esb8/4in-ECM/kicad/models/X322516MLB4SI.step

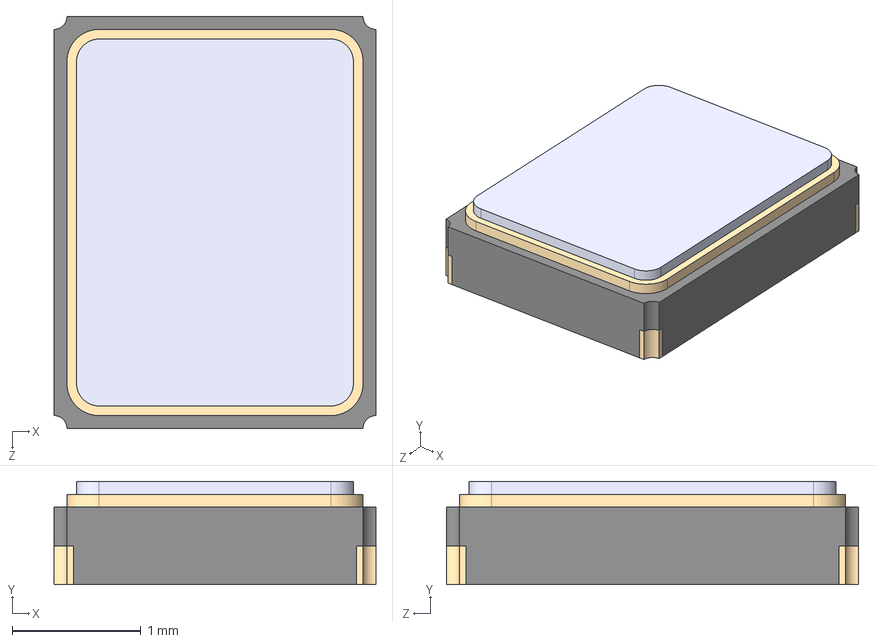
[picture p17: CAD file, 2025-09-10]
kicad/models/X322516MLB4SI.step
2.50 x 0.8 x 3.20 mm
